jiahuang/ant-farm/colony/src/build.py

# build file for the colony
# last byte is always FF for colonies

from random import randrange

# set up the id
MAX_ID = 65536 # FF FF
INCREMENTATION = 1
NUM_BYTES = 2
# MAX_DELAY = 255
# MIN_DELAY = 20

current_val = 1;
print "########### GENERATING COLONY ################# "

# read in the current id
with open("colony_id.c") as f:
  data = f.read().split("\n")[4:] # skip the first 5 lines
  val = ""
  for i, line in enumerate(reversed(data)):
    if len(line) > 1 and i >= 1:
      # parse out the hex
      val += line.split(" ")[2].replace("0x", "")#.decode("hex")
    
  current_val = int(val, 16)
  print "The current value is: ", current_val

# increment the current val
current_val += INCREMENTATION
if current_val > MAX_ID: current_val = 0 # wrap around
print "Incrementing id to: ", current_val
current_val = hex(current_val).replace("0x", "").upper()

# pad current value up to NUM_BYTES bytes long
if len(current_val) < NUM_BYTES*2:
  i = NUM_BYTES*2 - len(current_val) 
  while i > 0:
    current_val = "0"+current_val
    i -= 1

# split up current val into an array
print "HEX ID: ", current_val
current_vals = [current_val[i:i+2] for i in range(0, len(current_val), 2)]

with open('colony_id.c', 'w') as f:

  f.write("""/*
  * THIS IS AN AUTOGENERATED FILE.
  * DO NOT TOUCH.
  */

""")
  hex_id = []
  i = 1
  # print current_vals
  for val in reversed(current_vals):
    if len(val) == 1: val = "0" + val 
    f.write("#define ID_" + str(i) + " 0x"+str(val) + "\n")
    i += 1
